BadgePiratesLLC/BSidesKC_2022/Pic/_MG_3492.JPG

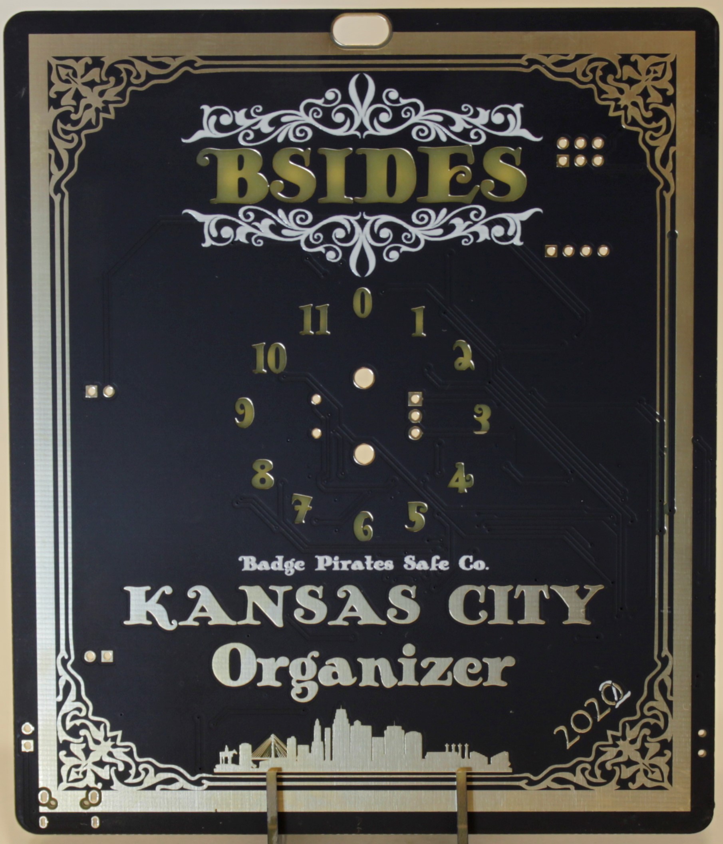
Pic/_MG_3492.JPG
