BadgePiratesLLC/BSidesKC_2022/Artwork/BsidesKC 2021/BSidesKC-Final_copy.png

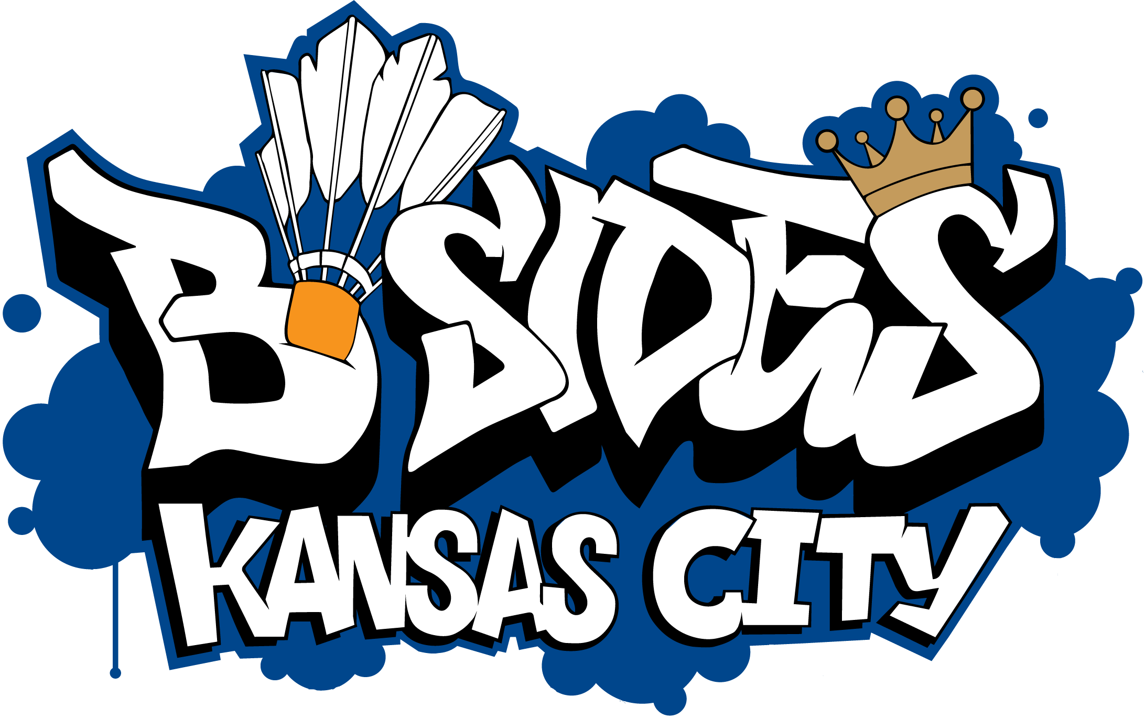
Artwork/BsidesKC 2021/BSidesKC-Final_copy.png
