BadgePiratesLLC/BSidesKC_2022/Artwork/BsidesKC 2021/unknown.png

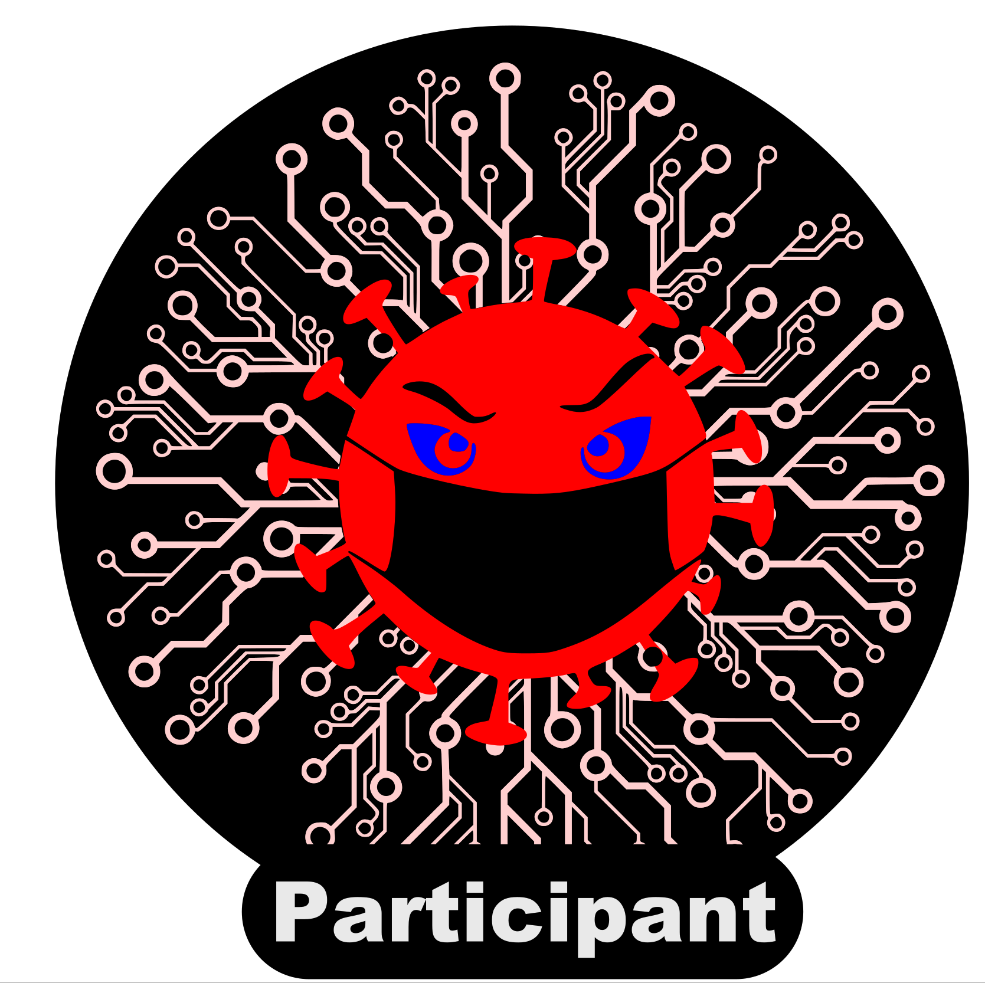
Artwork/BsidesKC 2021/unknown.png
