BadgePiratesLLC/BSidesKC_2022/CAD - Prototypes/.svg2shenzhen-cache/images/F.Cu_g1715.png

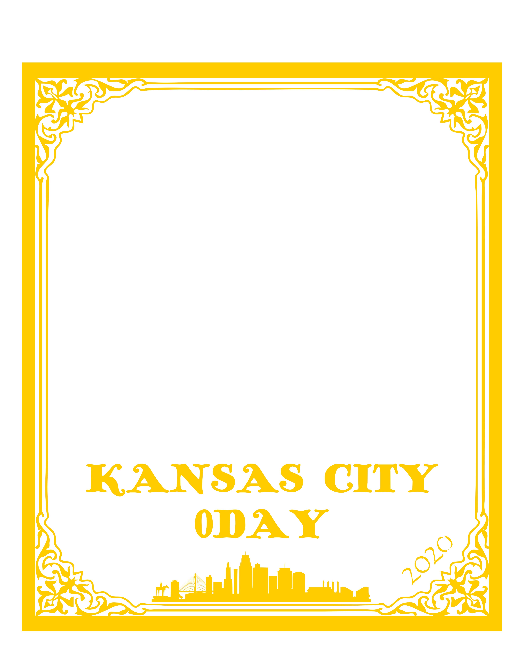
CAD - Prototypes/.svg2shenzhen-cache/images/F.Cu_g1715.png
