BadgePiratesLLC/BSidesKC_2022/CAD - Prototypes/BsidesKC 2022 SAO/.svg2shenzhen-cache/images/F.Cu_g31523.png

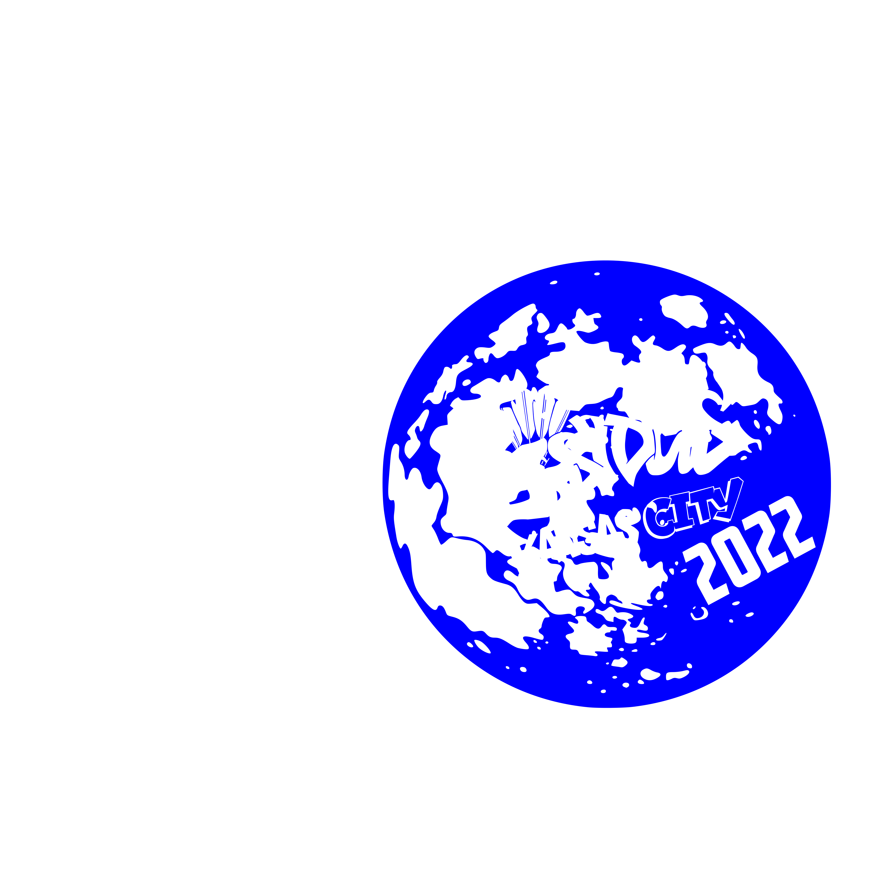
CAD - Prototypes/BsidesKC 2022 SAO/.svg2shenzhen-cache/images/F.Cu_g31523.png
