BadgePiratesLLC/BSidesKC_2022/CAD/BsidesKC SAO/.svg2shenzhen-cache/images/F.Cu_g9654.png

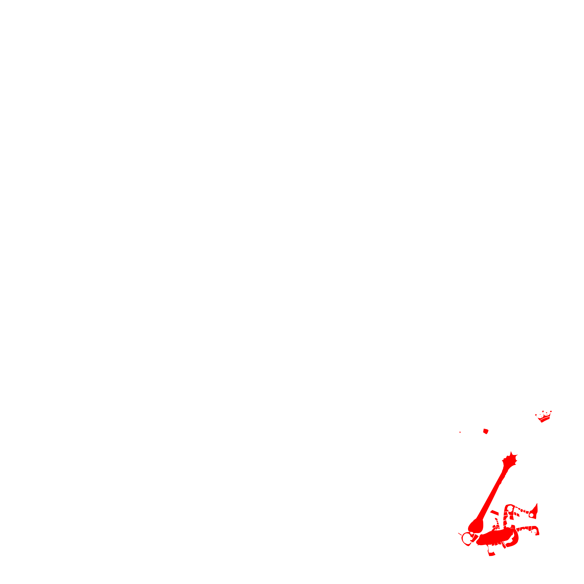
CAD/BsidesKC SAO/.svg2shenzhen-cache/images/F.Cu_g9654.png
