BadgePiratesLLC/BSidesKC_2022/CAD/BsidesKC SAO/BsidesKC 2022 SAO_front.png

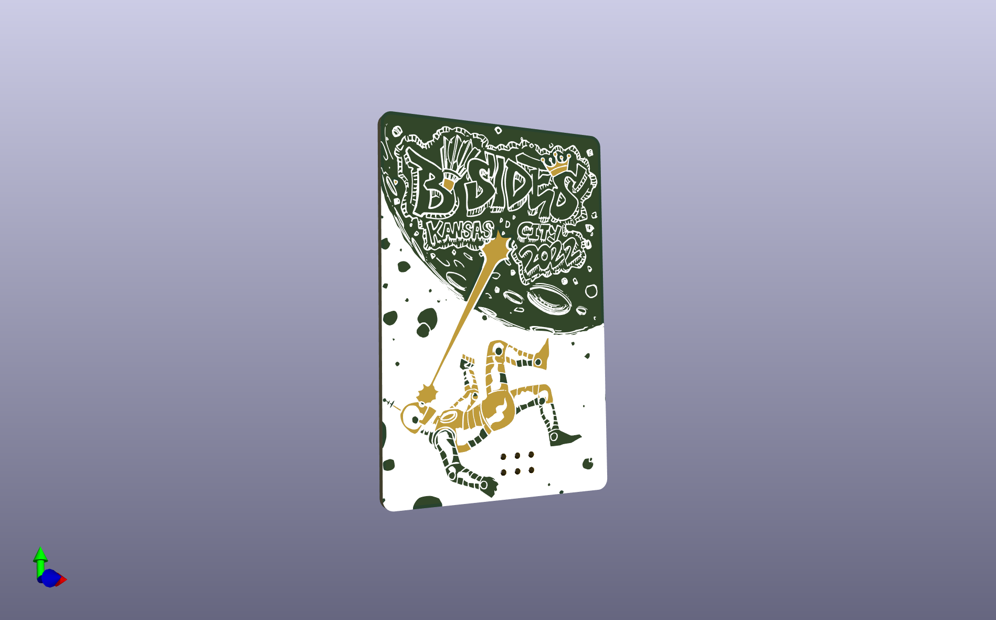
CAD/BsidesKC SAO/BsidesKC 2022 SAO_front.png
