BadgePiratesLLC/BSidesKC_2022/CAD/Gold SAOs/Arista-TGS/.svg2shenzhen-cache/images/F.Cu_g5240.png

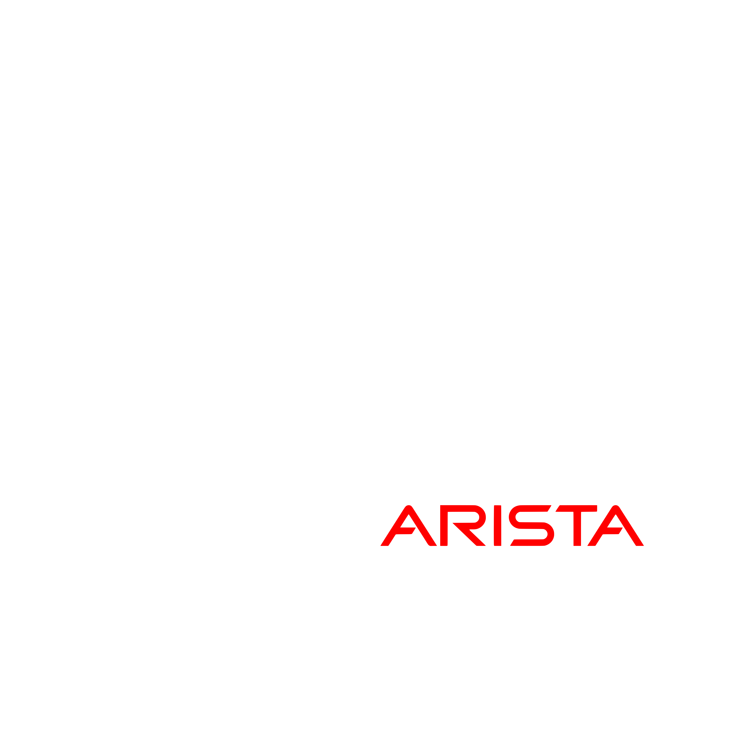
CAD/Gold SAOs/Arista-TGS/.svg2shenzhen-cache/images/F.Cu_g5240.png
