BadgePiratesLLC/BSidesKC_2022/CAD/Gold SAOs/Corelight/.svg2shenzhen-cache/images/F.Cu_g2224.png

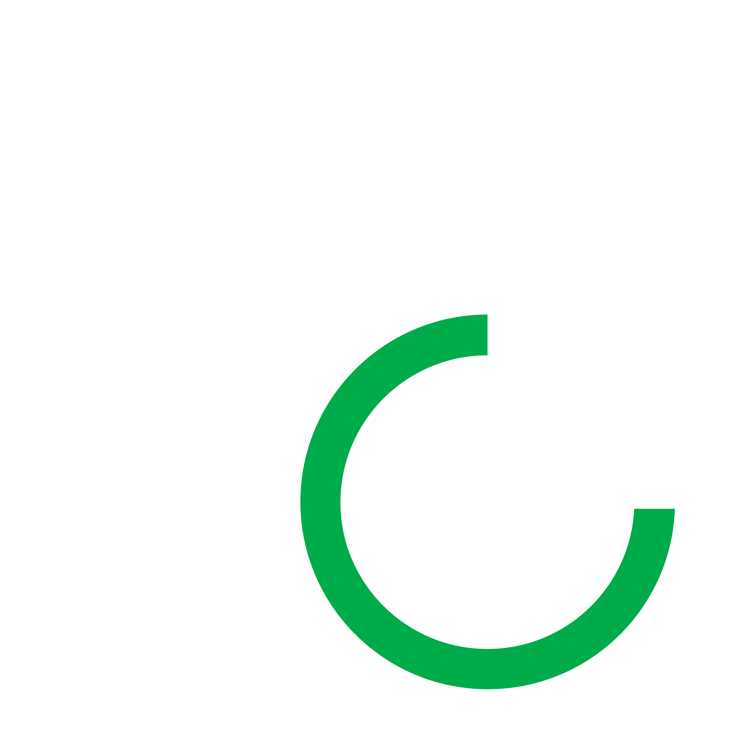
CAD/Gold SAOs/Corelight/.svg2shenzhen-cache/images/F.Cu_g2224.png
