BadgePiratesLLC/BSidesKC_2022/CAD/Gold SAOs/Red Canary/.svg2shenzhen-cache/images/F.Cu_g5240.png

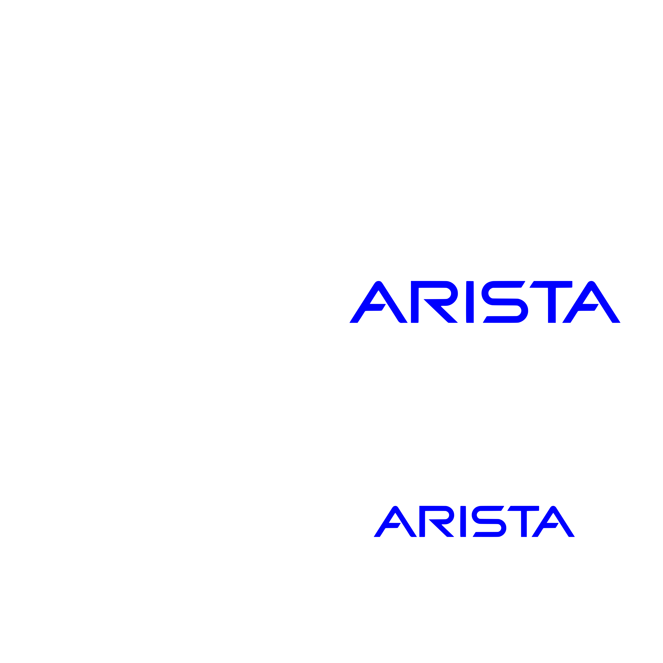
CAD/Gold SAOs/Red Canary/.svg2shenzhen-cache/images/F.Cu_g5240.png
