BadgePiratesLLC/BSidesKC_2022/Pic/_MG_3489.JPG

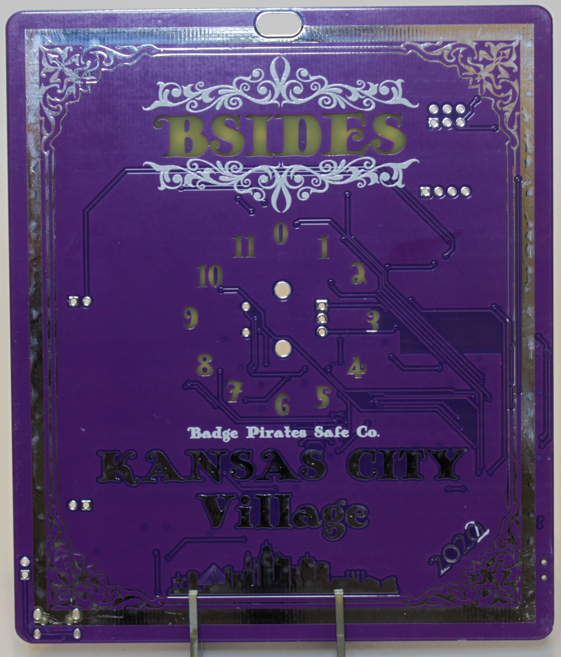
Pic/_MG_3489.JPG
