BadgePiratesLLC/BSidesKC_2022/Pic/_MG_3494.JPG

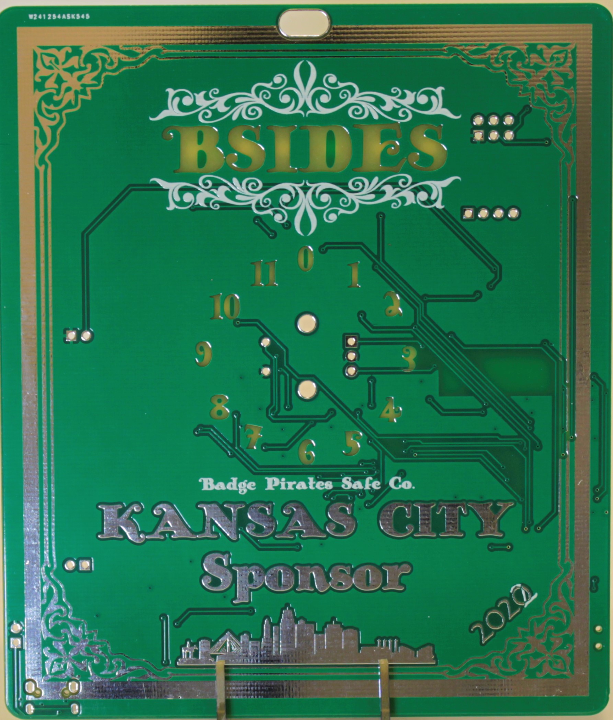
Pic/_MG_3494.JPG
