BadgePiratesLLC/BSidesKC_2022/Pic/_MG_3495.JPG

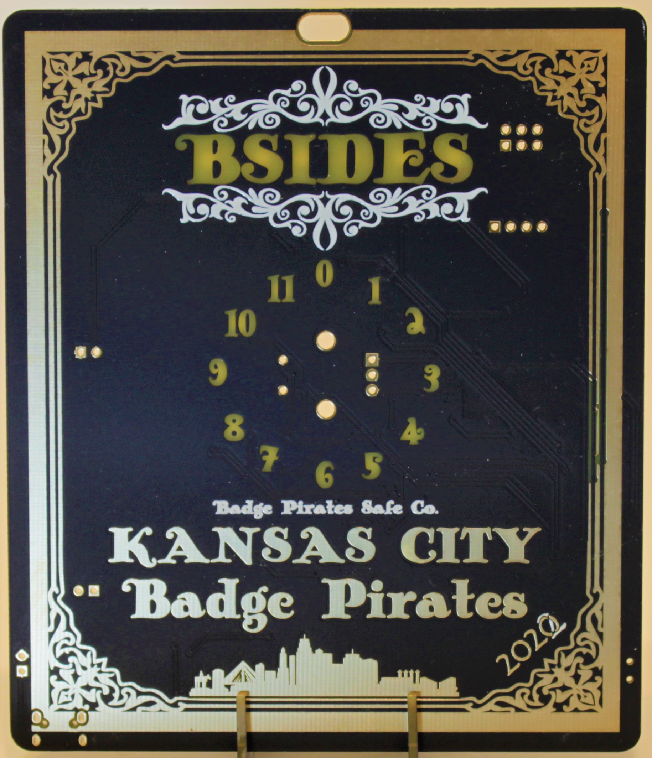
Pic/_MG_3495.JPG
