BadgePiratesLLC/BSidesKC_2022/Pic/_MG_3496.JPG

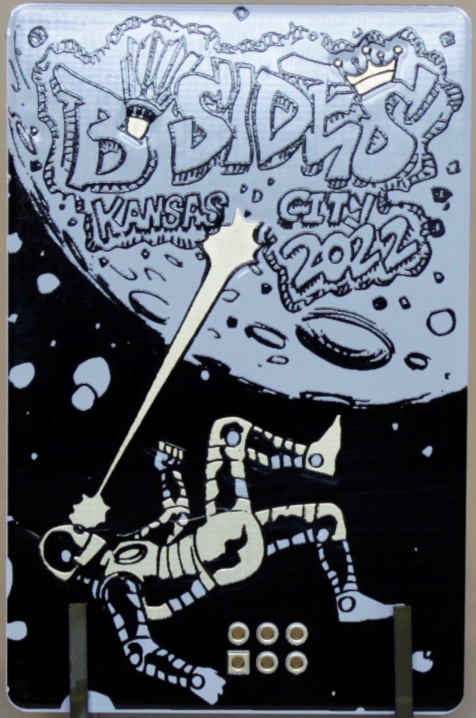
Pic/_MG_3496.JPG
