BadgePiratesLLC/BSidesKC_2022/CAD/BsidesKC-2022-Safe-Badge.kicad_pcb

## KiCad design CAD/BsidesKC-2022-Safe-Badge.kicad_pcb (2022-08-17)

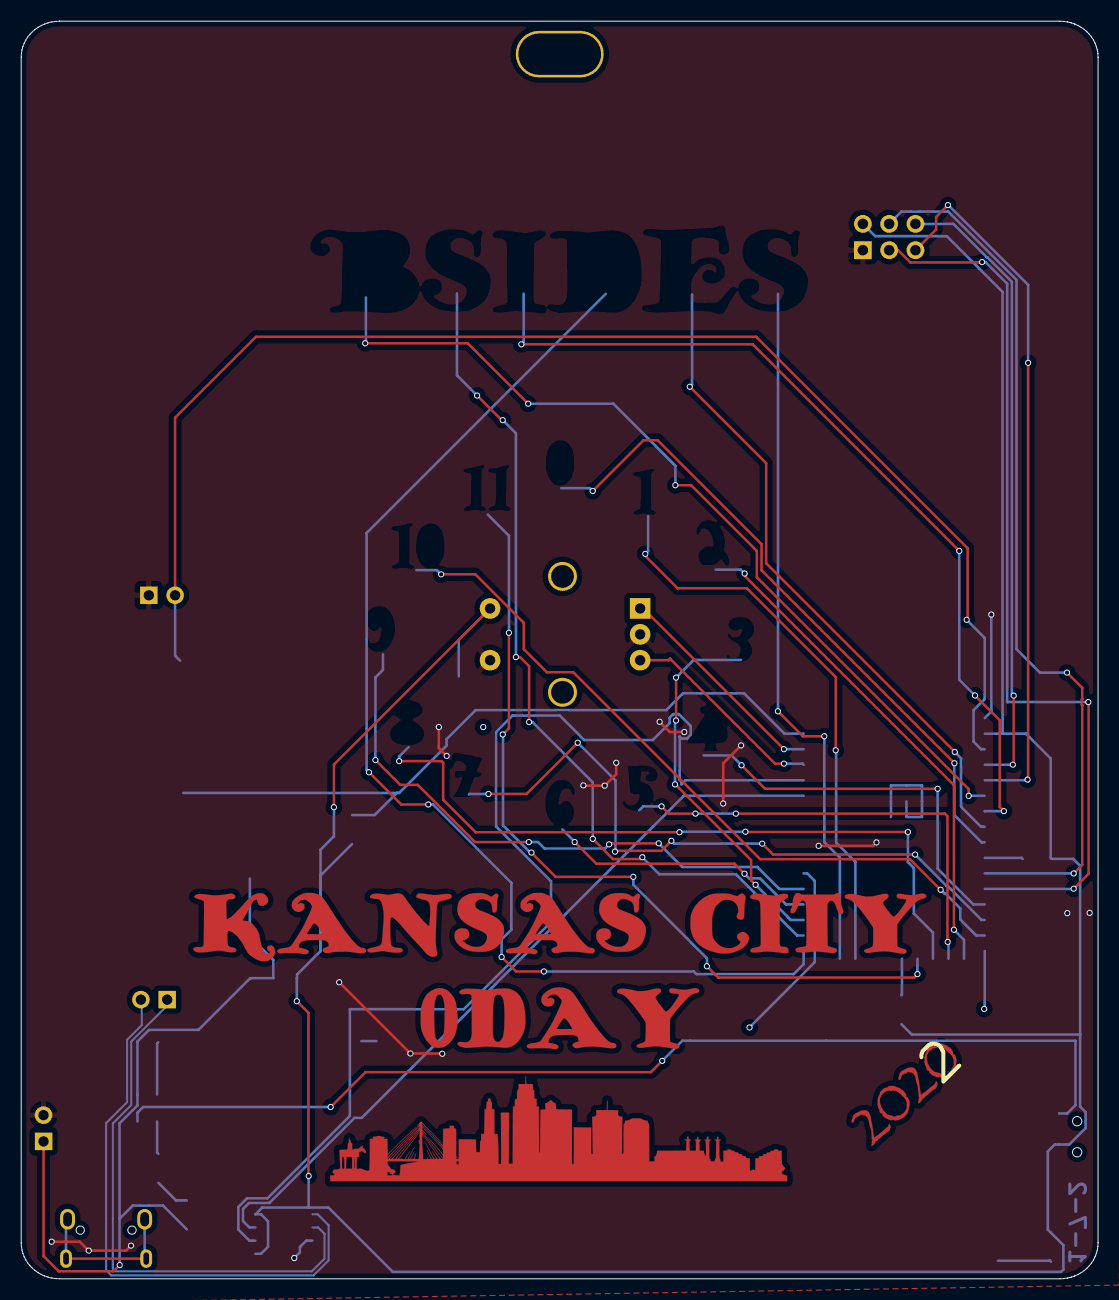
[picture p28: board BsidesKC-2022-Safe-Badge.kicad_pcb from above]

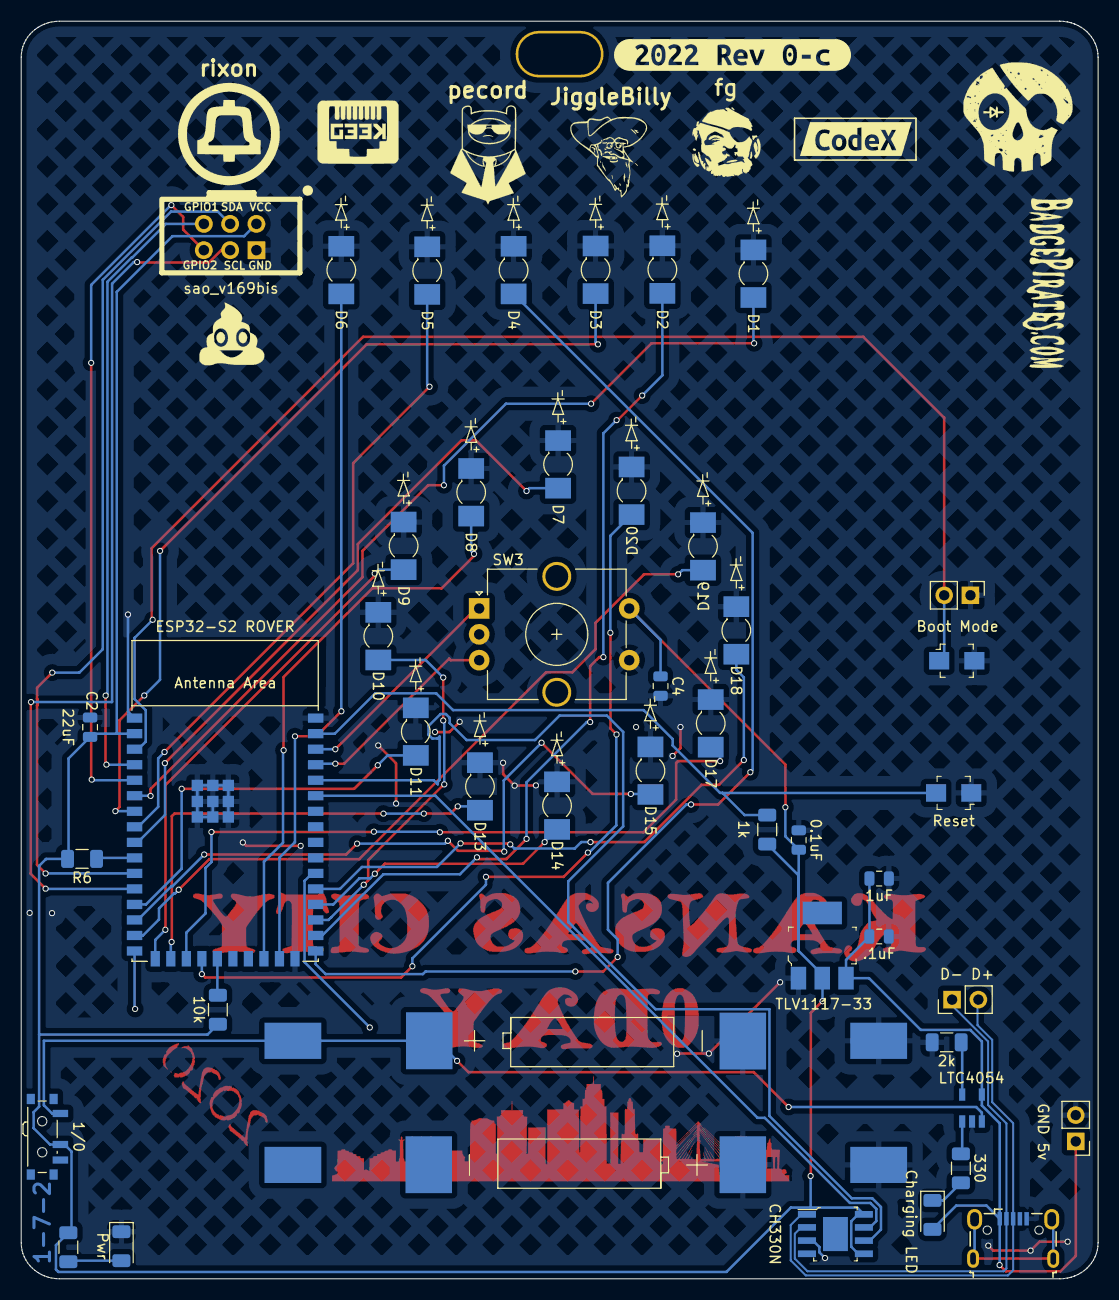
[picture p29: board BsidesKC-2022-Safe-Badge.kicad_pcb from below]

Board: 2 copper layers, 104.1 x 121.5 mm, 47 parts (28 on the bottom side), 40 nets.

Parts:
1/0: SW_SPDT; SW_SPDT_PCM12
BT1: Battery; AA
C1: 1uF; C_0805_2012Metric
C2: 22uF; C_0805_2012Metric
C3: 0.1uF; C_0805_2012Metric
C4, C5: .1uF; C_0805_2012Metric
D1, D2, D3, D4, D5, D6, D7, D8, D9, D10, D11, D13, D14, D15, D17, D18, D19, D20: LED; LED_Osram_Lx_P47F_D2mm_ReverseMount_Proper_Mask Only
D12: Charging LED; LED_1206_3216Metric
D16: Pwr; LED_1206_3216Metric
D- D+: Conn_01x02_Female; PinHeader_1x02_P2.54mm_Vertical
ESP32-S2 ROVER: ESP32-S2-WROOM; ESP32-S2-WROVER
GND 5v: 1x2; PinHeader_1x02_P2.54mm_Vertical
J2: 1x2; PinHeader_1x02_P2.54mm_Vertical
J4: USB_B_Mini; USB_Micro-B_Wuerth
R1: 2k; R_1206_3216Metric
R2: 330; R_1206_3216Metric
R3: R; R_1206_3216Metric
R4: 1k; R_1206_3216Metric
R5: 10k; R_1206_3216Metric
R6: R_Small_US; R_1206_3216Metric
Reset: Reset_Btn; Switch_Tactile_SMD_B3U-1000P-BPVersion
SW2: Boot Mode; Switch_Tactile_SMD_B3U-1000P-BPVersion
SW3: RotaryEncoder_Switch; RotaryEncoder_Alps_EC12E-Switch_Vertical_H20mm_CircularMoun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
U1: LTC4054
U3: CH330N; SOIC-8-1EP_W3.9mm
U4: TLV1117-33; SOT-223
X1: sao_v169bis; Badgelife-SAOv169-SAO_Side_B.SLK
kibuzzard-62C240C4: G***; kibuzzard-62C240C4
kibuzzard-62FC3E66: G***; kibuzzard-62FC3E66

Connections:
Boot: ESP32-S2 ROVER.3 (IO00), J2.2, SW2.1 (A)
D+: D- D+.2, J4.3 (D+), U3.1 (UD+)
D-: D- D+.1, J4.2 (D-), U3.2 (UD-)
GND: BT1.2 (-), C1.2, C2.2, C3.2, C4.2, C5.2, D1.1 (K), D2.1 (K), D3.1 (K), D4.1 (K), D5.1 (K), D6.1 (K), D7.1 (K), D8.1 (K), D9.1 (K), D10.1 (K), D11.1 (K), D13.1 (K), D14.1 (K), D15.1 (K), D16.1 (K), D17.1 (K), D18.1 (K), D19.1 (K), D20.1 (K), ESP32-S2 ROVER.1 (GND), ESP32-S2 ROVER.26 (GND), ESP32-S2 ROVER.42 (GND), ESP32-S2 ROVER.43 (GND), GND 5v.2, J2.1, J4.5 (GND), R1.2, Reset.1 (C), SW2.2 (B), SW3.C, SW3.S2, U1.2 (GND), U3.3 (GND), U4.1 (GND), X1.2 (GND)
IO01: ESP32-S2 ROVER.4 (IO01), X1.5 (GPIO1)
IO02: ESP32-S2 ROVER.5 (IO02), X1.6 (GPIO2)
IO03: D1.2 (A), ESP32-S2 ROVER.6 (IO03)
IO04: D3.2 (A), ESP32-S2 ROVER.7 (IO04)
IO05: D5.2 (A), ESP32-S2 ROVER.8 (IO05)
IO06: D7.2 (A), ESP32-S2 ROVER.9 (IO06)
IO07: ESP32-S2 ROVER.10 (IO07), R6.1
IO08: ESP32-S2 ROVER.11 (IO08), X1.3 (SDA)
IO09: ESP32-S2 ROVER.12 (IO09), X1.4 (SCL)
IO10: D11.2 (A), ESP32-S2 ROVER.13 (IO10)
IO11: D15.2 (A), ESP32-S2 ROVER.14 (IO11)
IO12: D19.2 (A), ESP32-S2 ROVER.15 (IO12)
IO14: D9.2 (A), ESP32-S2 ROVER.17 (IO14)
IO15: D13.2 (A), ESP32-S2 ROVER.18 (IO15)
IO16: D17.2 (A), ESP32-S2 ROVER.19 (IO16)
IO17: D20.2 (A), ESP32-S2 ROVER.20 (IO17)
IO21: D8.2 (A), ESP32-S2 ROVER.24 (IO21)
IO26: D6.2 (A), ESP32-S2 ROVER.25 (IO26)
IO33: D4.2 (A), ESP32-S2 ROVER.27 (IO33)
IO34: D2.2 (A), ESP32-S2 ROVER.28 (IO34)
IO35: D10.2 (A), ESP32-S2 ROVER.29 (IO35)
IO36: D14.2 (A), ESP32-S2 ROVER.30 (IO36)
IO37: D18.2 (A), ESP32-S2 ROVER.31 (IO37)
IO45: ESP32-S2 ROVER.39 (IO45), SW3.B
IO46: ESP32-S2 ROVER.40 (IO46), SW3.A
unnamed: 1/0.1 (A), BT1.1 (+), U1.3 (BAT)
unnamed: D12.1 (K), R2.1
unnamed: D16.2 (A), R3.2
unnamed: R1.1, U1.5 (PROG)
unnamed: R2.2, U1.1 (~CHRG)
unnamed: ESP32-S2 ROVER.21 (IO18), R5.1
RESET: ESP32-S2 ROVER.41 (EN), R4.2, Reset.2 (D)
USB_RX_ESP_TX: ESP32-S2 ROVER.37 (TXD0), U3.7 (RXD)
USB_TX_ESP_RX: ESP32-S2 ROVER.38 (RXD0), U3.6 (TXD)
VBUS: C1.1, C5.1, D12.2 (A), GND 5v.1, J4.1 (VBUS), U1.4 (VCC), U4.3 (VI)
VCC: 1/0.2 (B), C2.1, C3.1, C4.1, ESP32-S2 ROVER.2 (3V3), R3.1, R4.1, R5.2, R6.2, SW3.S1, U3.5 (VCC), U3.8 (V3), U4.2 (VO), X1.1 (VCC)
