BadgePiratesLLC/BSidesKC_2022/code/BlinkyLights/BlinkyLights.ino

void setup() {
  // put your setup code here, to run once:
pinMode(3,OUTPUT);
pinMode(34,OUTPUT);
pinMode(4,OUTPUT);
pinMode(33,OUTPUT);
pinMode(5,OUTPUT);
pinMode(26,OUTPUT);
pinMode(6,OUTPUT);
pinMode(21,OUTPUT);
pinMode(14,OUTPUT);
pinMode(35,OUTPUT);
pinMode(10,OUTPUT);
pinMode(15,OUTPUT);
pinMode(36,OUTPUT);
pinMode(11,OUTPUT);
pinMode(16,OUTPUT);
pinMode(37,OUTPUT);
pinMode(12,OUTPUT);
pinMode(17,OUTPUT);

Serial.begin(115200);

}

void loop() {
  // put your main code here, to run repeatedly:
digitalWrite(3,HIGH);
delay(25);
digitalWrite(3,LOW);
delay(25);
digitalWrite(34,HIGH);
delay(25);
digitalWrite(34,LOW);
delay(25);
digitalWrite(4,HIGH);
delay(25);
digitalWrite(4,LOW);
delay(25);
digitalWrite(33,HIGH);
delay(25);
digitalWrite(33,LOW);
delay(25);
digitalWrite(5,HIGH);
delay(25);
digitalWrite(5,LOW);
delay(25);
digitalWrite(26,HIGH);
delay(25);
digitalWrite(26,LOW);
delay(25);

digitalWrite(26,HIGH);
delay(25);
digitalWrite(26,LOW);
delay(25);
digitalWrite(5,HIGH);
delay(25);
digitalWrite(5,LOW);
delay(25);
digitalWrite(33,HIGH);
delay(25);
digitalWrite(33,LOW);
delay(25);
digitalWrite(4,HIGH);
delay(25);
digitalWrite(4,LOW);
delay(25);
digitalWrite(34,HIGH);
delay(25);
digitalWrite(34,LOW);
delay(25);
digitalWrite(3,HIGH);
delay(25);
digitalWrite(3,LOW);
delay(25);

digitalWrite(6,HIGH);
delay(25);
digitalWrite(6,LOW);
delay(25);
digitalWrite(21,HIGH);
delay(25);
digitalWrite(21,LOW);
delay(25);
digitalWrite(14,HIGH);
delay(25);
digitalWrite(14,LOW);
delay(25);
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
digitalWrite(11,LOW);delay(25);
digitalWrite(36,LOW);delay(25);
digitalWrite(15,LOW);delay(25);
digitalWrite(10,LOW);delay(25);
digitalWrite(35,LOW);delay(25);
digitalWrite(14,LOW);delay(25);
digitalWrite(21,LOW);delay(25);
digitalWrite(6,LOW);delay(25);

Serial.println ("sucks");
}
